dg3qq/af_two-tone-gen-f07/F07-project/doc/pdf/ad_mic_con_icom_ic706.pdf

Mikrofon-Anschluß f. ICOM IC-706 u.ä. PIN | Signal | Farbe

1 +8V !!max. 10mA rot
2 UP/DOWN | blau
3 AUDIO OUT | n/a
4 PTT | | gelb
5 MIC GROUND | grau
6 MIC | | weiss
7 GROUND/EARTH grün
8 SQUELCH braun

note +8V nicht strombegrenzt - Bei Überstrom TRX kaput !

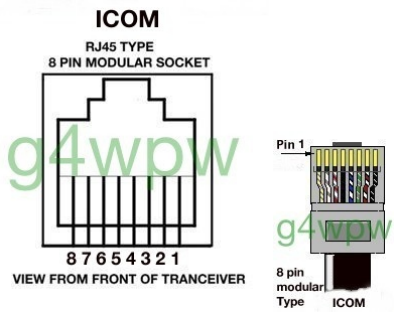
[picture p20: figure]

### ICOM HM103

1

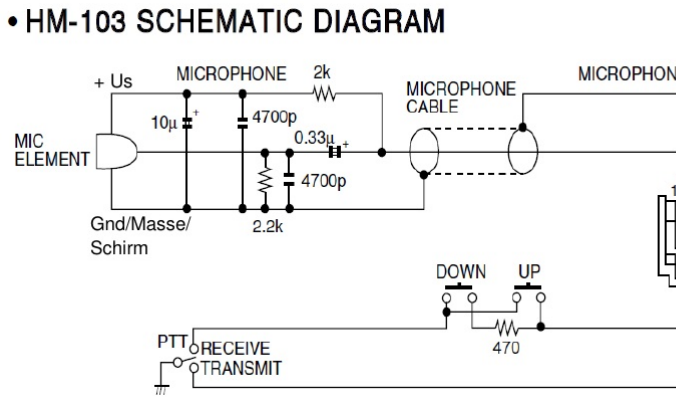
[picture p21: figure]

g4wpw (https://www.qsl.net/g4wpw/date.html)

2
