dg3qq/af_two-tone-gen-f07/F07-project/doc/pdf/ad_mic_con_kenwood_ts700.pdf

Mikrofon-Anschluß f. KENWOOD TS-700G u.ä. PIN Signal

1 MIC
2 PTT
3 PTT GND
4 MIC GND

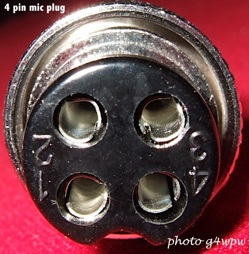
[picture p22: figure]

kenwood MC-10

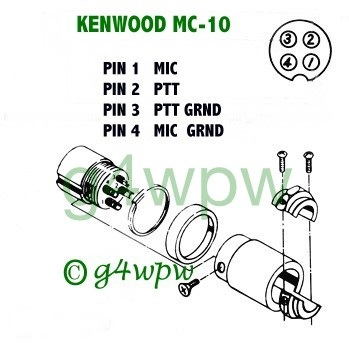
[picture p23: figure]

g4wpw (https://www.qsl.net/g4wpw/date.html)

1
