dg3qq/af_two-tone-gen-f07/F07-project/doc/pdf/ad_mic_con_yaesu_.pdf

# Mikrofon-Anschluß f. YAESU FT-290R u.ä. PIN Signal

1 MIC Schirm/Masse
2 MIC
3 PTT
4 + 12VOLT ( + 5 VOLTS FT730-FT290R ) 5 SPEAKER
6 UP
7 DOWN

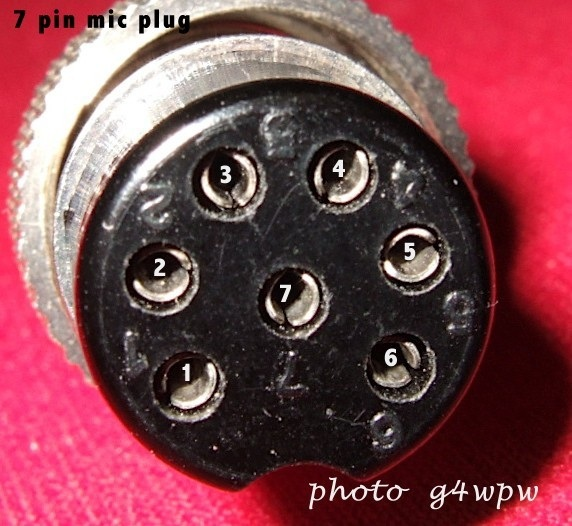
[picture p24: figure]

### yaesu YM-47

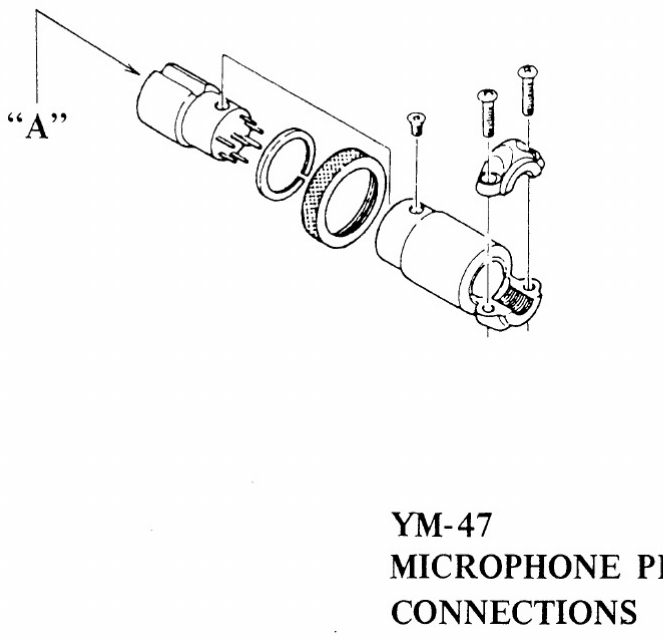
[picture p25: figure]

### yaesu YM-49

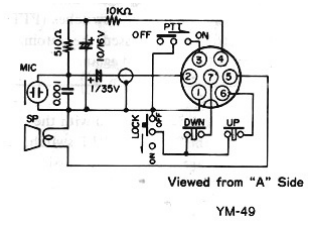
[picture p26: figure]

g4wpw (https://www.qsl.net/g4wpw/date.html)
