dg3qq/af_two-tone-gen-f07/F07-project/ad_mic_con_kenwood_ts-700/KENWOOD_MC10.pdf

MC10 | https://www.qsl.net/g4wpw/mc10.html

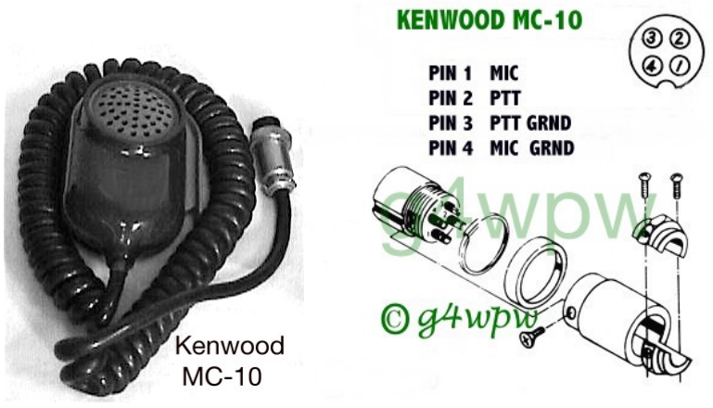
[picture p32: figure]

1 von 1 | 24.07.22, 16:05
