dg3qq/af_two-tone-gen-f07/F07-project/ad_mic_con/!!!Mic_Plug_Positions.jpg

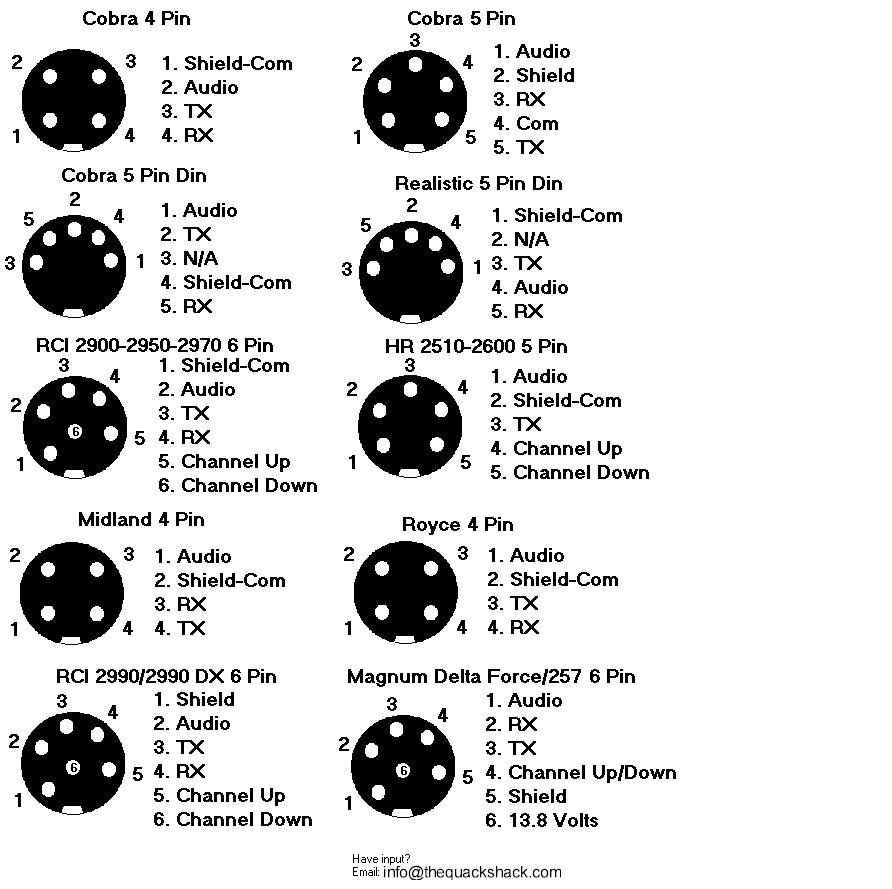
F07-project/ad_mic_con/!!!Mic_Plug_Positions.jpg
