dg3qq/af_two-tone-gen-f07/F07-project/ad_mic_con_icom_ic706/ichm8.jpg

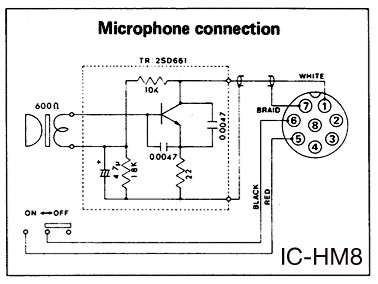
F07-project/ad_mic_con_icom_ic706/ichm8.jpg
