dg3qq/af_two-tone-gen-f07/F07-project/ad_mic_con_icom_ic7300/IC-7300_Mic-in.webp

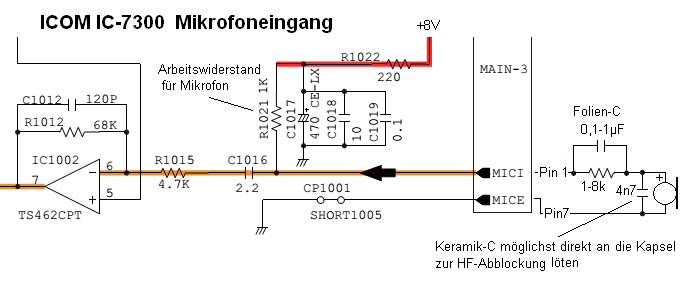
F07-project/ad_mic_con_icom_ic7300/IC-7300_Mic-in.webp
