dg3qq/af_two-tone-gen-f07/F07-project/ad_mic_con_icom_ic7300/ICOM-Elec-Mic1a.JPG

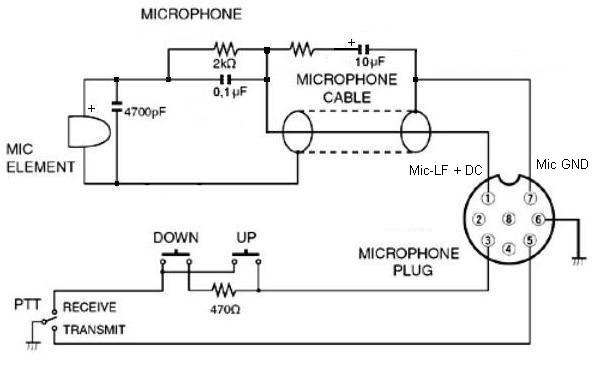
F07-project/ad_mic_con_icom_ic7300/ICOM-Elec-Mic1a.JPG
