dg3qq/af_two-tone-gen-f07/F07-project/ad_mic_con_yaesu_ft817/mh31p.jpg

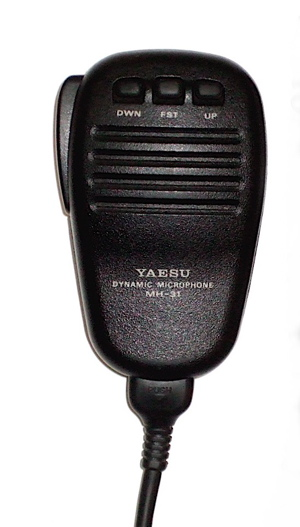
F07-project/ad_mic_con_yaesu_ft817/mh31p.jpg
