dg3qq/af_two-tone-gen-f07/F07-project/ad_mic_con_yaesu_ft817/MH-31_dyn2elektret_3.jpg

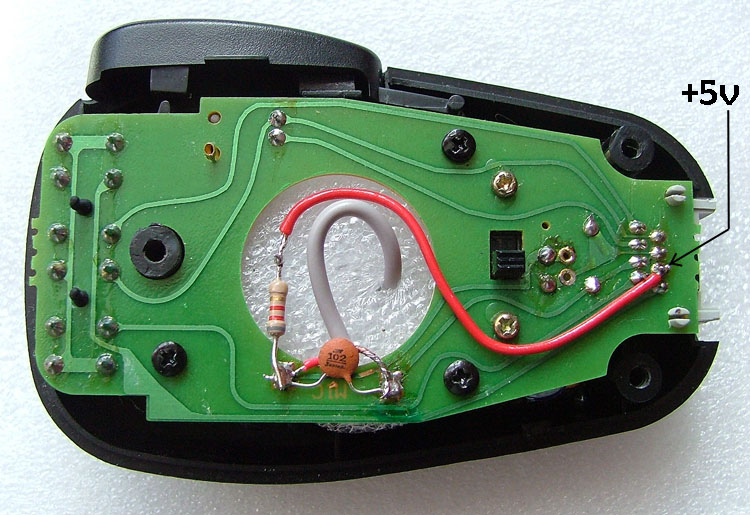
F07-project/ad_mic_con_yaesu_ft817/MH-31_dyn2elektret_3.jpg
