dg3qq/af_two-tone-gen-f07/F07-project/asset/20240112_182957-25.jpg

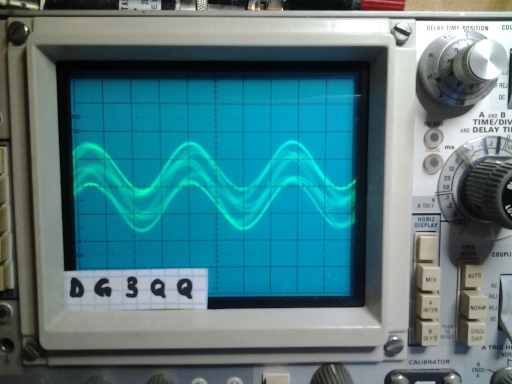
F07-project/asset/20240112_182957-25.jpg
