dg3qq/af_two-tone-gen-f07/F07-project/asset/IMAGE1.BMP

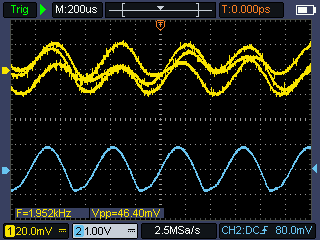
F07-project/asset/IMAGE1.BMP
