dg3qq/af_two-tone-gen-f07/F07-project/asset/twin_t_principle.gif

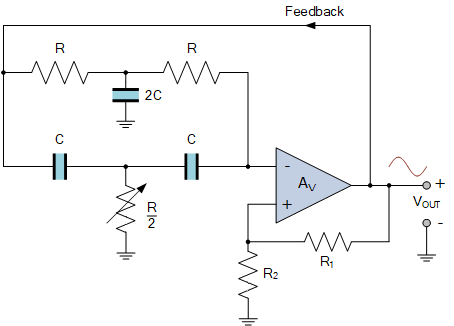
F07-project/asset/twin_t_principle.gif
