dg3qq/af_two-tone-gen-f07/F07-project/asset/two_tone#1_Gerber_Viewer_PCB-Prototype.png

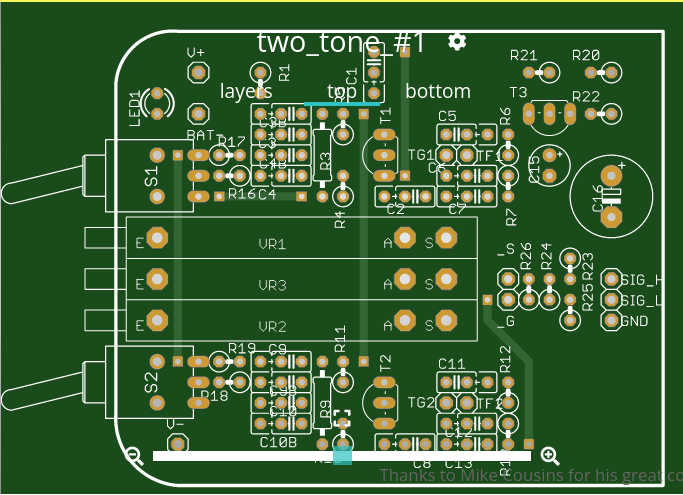
F07-project/asset/two_tone#1_Gerber_Viewer_PCB-Prototype.png
