dg3qq/af_two-tone-gen-f07/F07-project/asset/two_tone_#1_cs.png

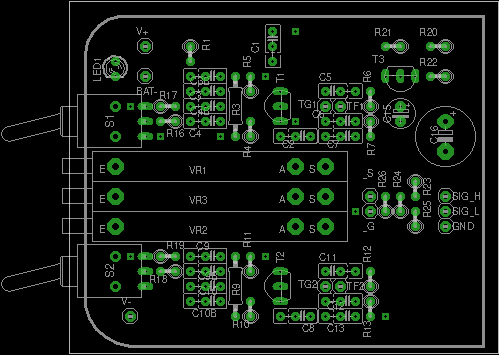
F07-project/asset/two_tone_#1_cs.png
