dg3qq/af_two-tone-gen-f07/F07-project/asset/Zweiton.jpg

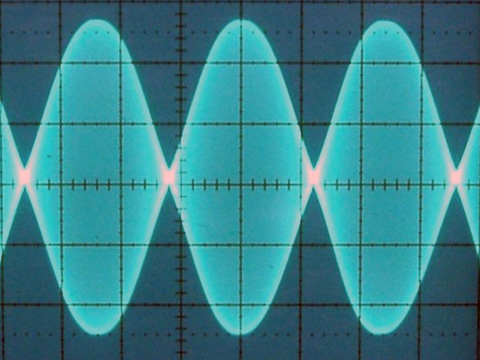
F07-project/asset/Zweiton.jpg
