dg3qq/af_two-tone-gen-f07/pictures/20221222_141324.jpg

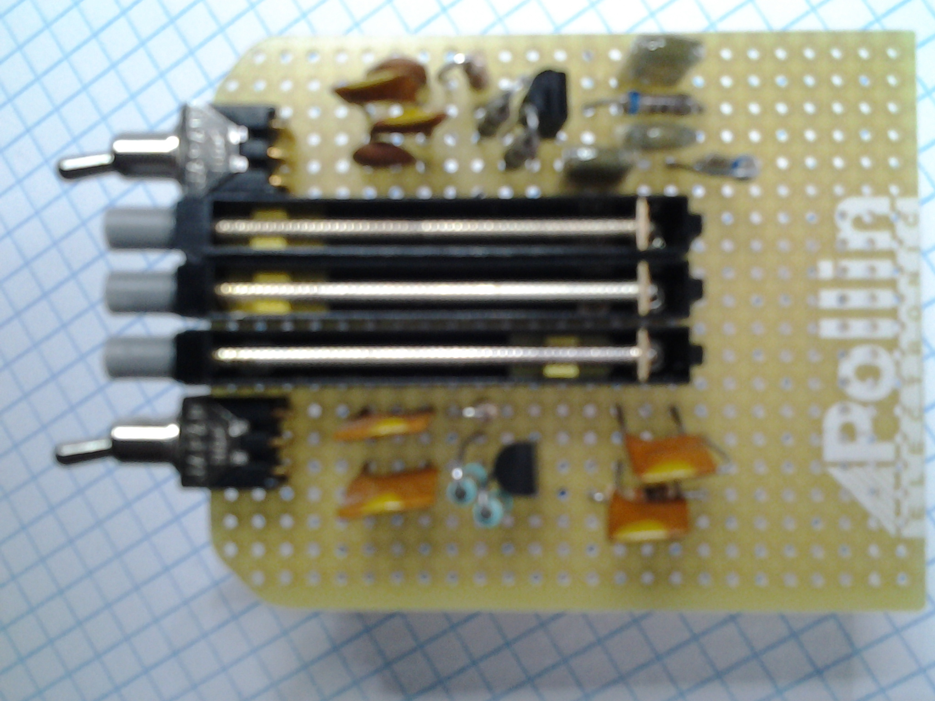
pictures/20221222_141324.jpg
