dg3qq/af_two-tone-gen-f07/pictures/20230105_000310.jpg

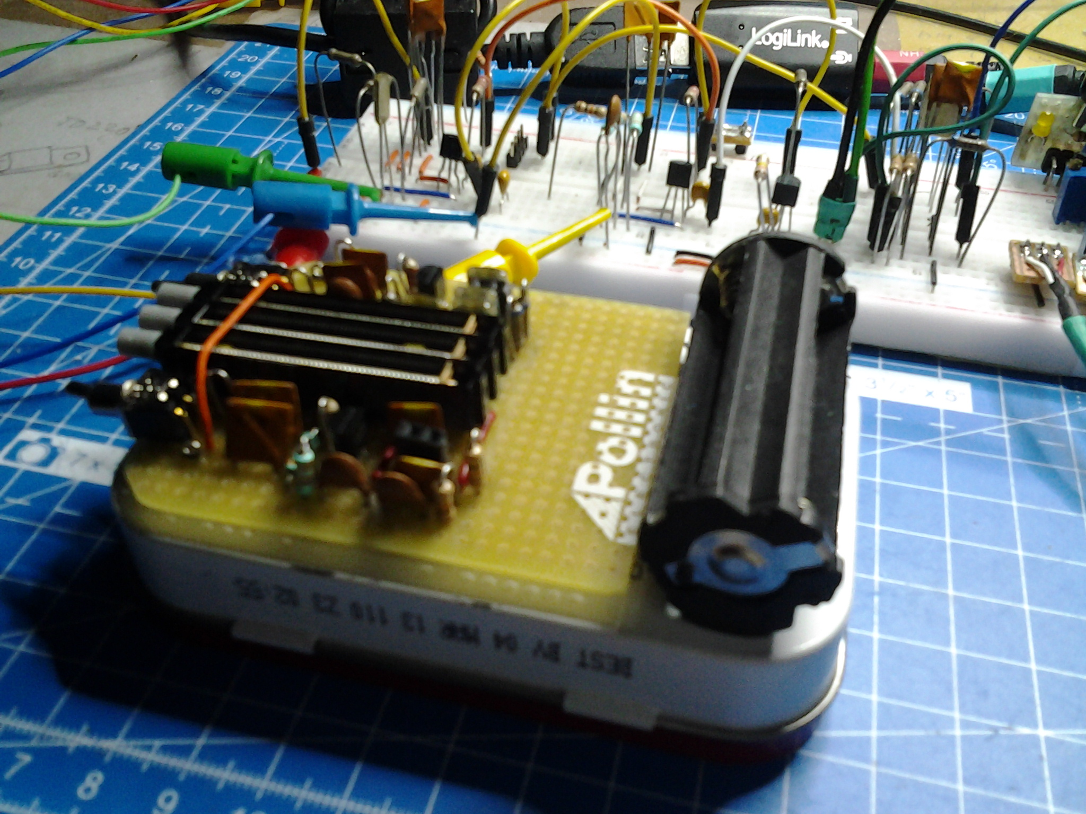
pictures/20230105_000310.jpg
