dg3qq/af_two-tone-gen-f07/pictures/20231218_160651.jpg

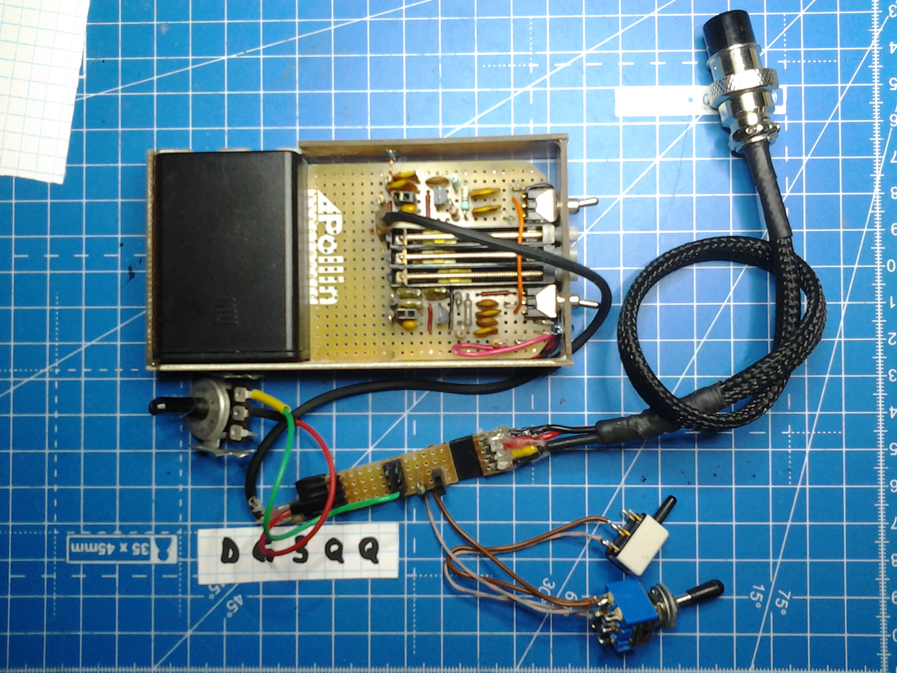
pictures/20231218_160651.jpg
