dg3qq/af_two-tone-gen-f07/pictures/20231218_160700.jpg

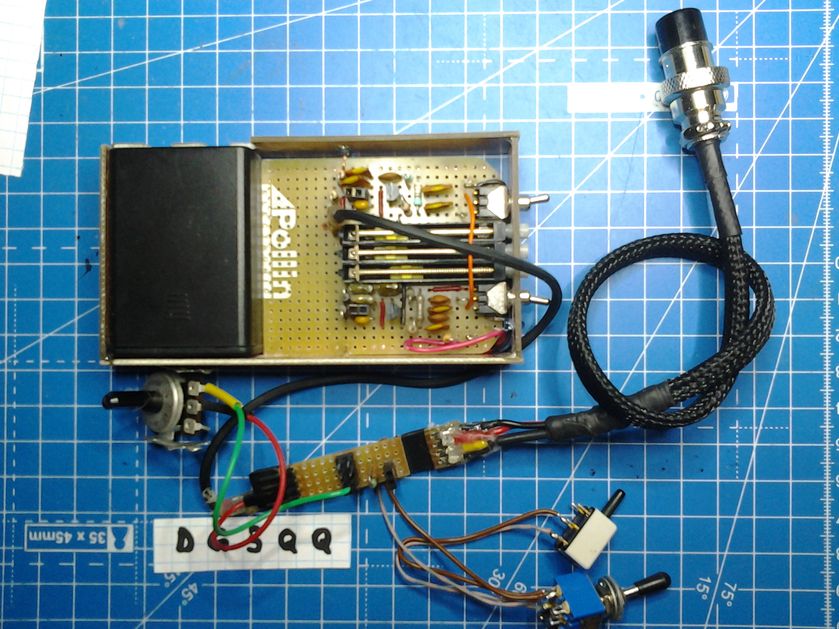
pictures/20231218_160700.jpg
