dg3qq/af_two-tone-gen-f07/pictures/20240103_195503-25.jpg

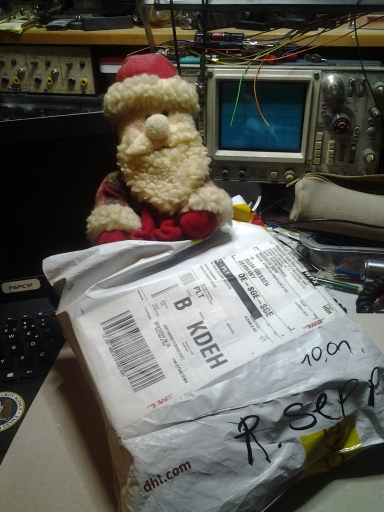
pictures/20240103_195503-25.jpg
