dg3qq/af_two-tone-gen-f07/pictures/20240111_224005-25.jpg

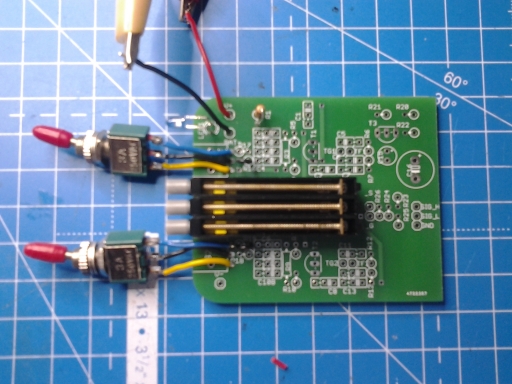
pictures/20240111_224005-25.jpg
