dg3qq/af_two-tone-gen-f07/pictures/20240112_182855.jpg

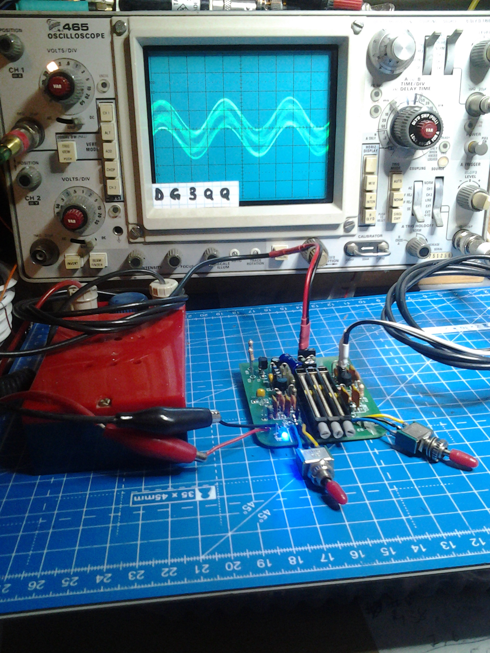
pictures/20240112_182855.jpg
