dg3qq/af_two-tone-gen-f07/pictures/20240112_182911-25.jpg

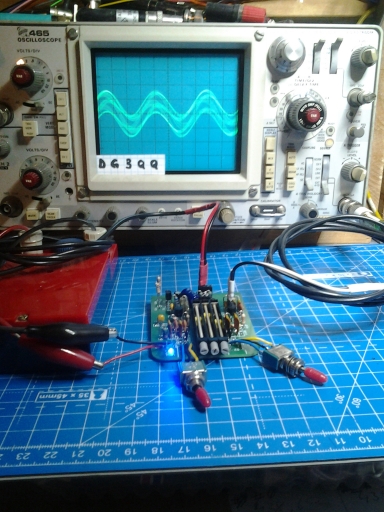
pictures/20240112_182911-25.jpg
