dg3qq/af_two-tone-gen-f07/pictures/w_psu_linreg.jpg

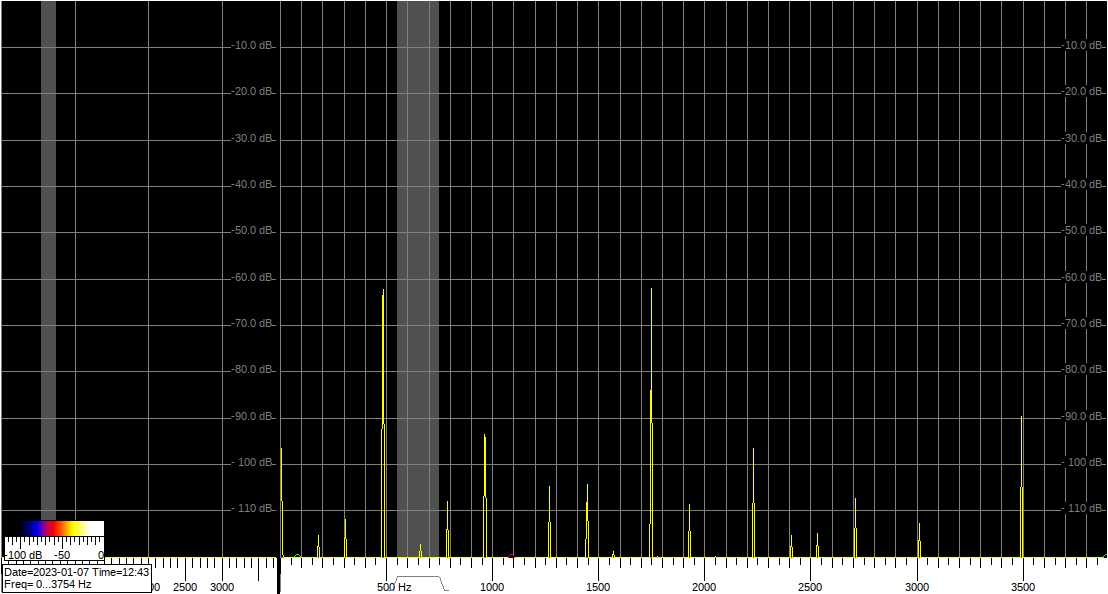
pictures/w_psu_linreg.jpg
