dg3qq/af_two-tone-gen-f07/af_two-tone-gen#1_LTspice/af_two_tone_0v03.asc

C1: cap; {ct_1}
C2: cap; {ct_1}
C3: cap; {ct_1}
Q1: npn; 2N3904
R1: res; {rt_1}
R2: res; {rt_1}
R4: res; 680k
R5: res; 2k2
R6: res; .1
V1: voltage; 6
Named nets: 0, fo_1
.param rt_1 4k7
.param ct_1=10n
.tran 0 100m 0 startup
https://electronics.stackexchange.com/questions/636489/bjt-phase-shift-oscillator
