dg3qq/af_two-tone-gen-f07/af_two-tone-gen#1_LTspice/af_two_tone_0v05.asc

C1: cap; {ct_1}
C2: cap; {ct_1}
C3: cap; {ct_1}
C4: polcap; 10µ
Q1: npn; 2N3904
R1: res; {rt_1}
R2: res; {rt_1}
R3: res; {rt_1}
R4: res; 10k
R5: res; 47k
R6: res; 680
R7: res; 2k2
V1: voltage; {Vcc}
Named nets: 0, fo_1
.param rt_1 4k7
.param ct_1=4n7
.tran 0 100m 0 startup
https://electronics.stackexchange.com/questions/636489/bjt-phase-shift-oscillator
The frequency of oscillation Fr = 1/(2 pi RC sqrt 2N)
 
Where:
Fr is the Output Frequency in Hertz
R is the Resistance in Ohms
C is the Capacitance in Farads
N is the number of RC stages. (N = 3)
.step param Vcc list 7 9 12
.fourier {Freq} V(fo_1)
https://www.circuitsgallery.com/rc-phase-shift-oscillator-using-transistor/
