dg3qq/af_two-tone-gen-f07/af_two-tone-gen#1_LTspice/twin-t-osc-0v01.asc

C1: cap; 10n
C2: cap; 10n
C3: cap; 22n
Q1: npn; 2N3904
R1: res; {Rv}
R2: res; 33k
R3: res; 33k
R4: res; 100k
V1: voltage; 9
Named nets: 0, out, tap
R2 = R3 = 2+R1
.tran 0 .2 0.1
.step param Rv list 2k 10k
f = 1/( 2pi  RC)
C1 = C2 = C3 /2
