dg3qq/af_two-tone-gen-f07/af_two-tone-gen#1_LTspice/twin-t-osc-0v02.asc

C1: cap; {Co1}
C2: cap; {Co1}
C3: cap; 22n
C4: cap; 1µ
C5: cap; 22n
C6: cap; 22n
C7: polcap; 10µ
C8: cap; 10n
D1: zener; 1N746
D2: zener; 1N751
D3: diode; 1N4148
Q1: npn; 2N3904
Q2: npn; 2N3904
R1: res; {Rv}
R2: res; {Ro1}
R3: res; {Ro1}
R4: res; 10k
R5: res; 10k
R6: res; 4k7
R7: res; 8k2
R8: res; 8k2
R9: res; 1k2
R10: res; 1k2
R11: res; 22k
R12: res; 10k
R13: res; 15k
V1: voltage; 9
Named nets: 0, out, tap, Vcc, V_b
R2 = R3 = 2+R1
.tran 0 0.4 0.2
.step param Rv list 8k 9k 10k
f = 1/( 2pi  RC)
C1 = C2 = C3 /2
5v1
K7QO noise
f = 1/( 2pi * RC)
.param Ro1 = 33k
.param Co1=10n
