dg3qq/af_two-tone-gen-f07/af_two-tone-gen#1_LTspice/twin-t-osc-0v05.asc

C1: cap; {Co1}
C2: cap; {Co1}
C3: cap; {2*Co1}
C4: cap; 1µ
C5: cap; {Cf1}
C6: cap; {Cf1}
C7: polcap; 10µ
C8: cap; 10n
C9: cap; {Co2}
C10: cap; {Co2}
C11: cap; {2* Co2}
C12: cap; 1µ
C13: cap; {Cf2}
C14: cap; {Cf2}
D1: zener; 1N746
D2: zener; 1N751
D3: diode; 1N4148
D4: diode; 1N4148
Q1: npn; 2N3904
Q2: npn; 2N3904
Q3: npn; 2N3904
R1: res; {Rv1}
R2: res; {Ro1}
R3: res; {Ro1}
R4: res; 10k
R5: res; 10k
R6: res; 4k7
R7: res; {Rf1}
R8: res; {Rf1}
R9: res; 1k2
R10: res; 1k2
R11: res; 22k
R12: res; 10k
R13: res; 15k
R14: res; {Rv2}
R15: res; {Ro2}
R16: res; {Ro2}
R17: res; 10k
R18: res; 10k
R19: res; {Rf2}
R20: res; {Rf2}
R21: res; 10k
R22: res; 15k
R23: res; 10k
R24: res; 560
R25: res; 5k6
R26: res; 22k
R27: res; 560
R28: res; 6k8
R29: res; 2k2
R30: res; 680
R31: res; 220
R32: res; 68
R33: res; 33
V1: voltage; 9
Named nets: 0, f1_out, tap1, Vcc, V_b, f2_out, tap2, out_L, out_H, T_0dB, T_10dB, T_20dB, T_30dB, T_40dB, T_50dB
R2 = R3 = 2+R1
.tran 0 1 0.2
.step param Rv1 list 5k 8k 10k 15k
f = 1/( 2pi  RC)
C1 = C2 = C3 /2
5v1
K7QO noise
f = 1/( 2pi * RC)
.param Ro1 = 47k
.param Co1=10n
f = 1/( 2pi * RC)
.step param Rv2 list 3k3 4k7 8k 10k
.param Ro2 = 33k
.step param Co2 list 1n 2n2 3n3 4n7
.param Cf2=3n3
.param Cf1=22n
.param Rf1=10k
.param  Rf2=18k
.param Rv2=5k
.param Rv1=10k
.param Cf1=22n
C3=22n
.param Co2=3n3
.param Ro1 = 47k
18k, 3n3;  fc = 2680 [Hz]
http://sim.okawa-denshi.jp/en/CRCRtool.php
10k, 22n;  fc = 723.4[Hz]
